Mic-Tsai/Power_Consumption_Current_Sense_System-V2/example/Python_Plot/ex1/ch1_iload-1111.png

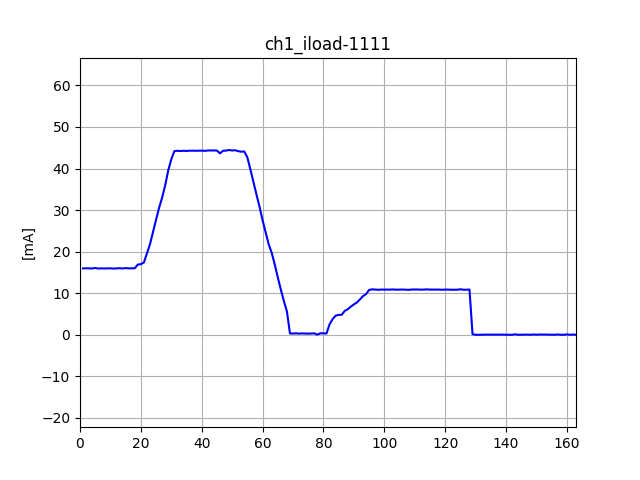
example/Python_Plot/ex1/ch1_iload-1111.png
