Mic-Tsai/Power_Consumption_Current_Sense_System-V2/res/ch1_iload.png

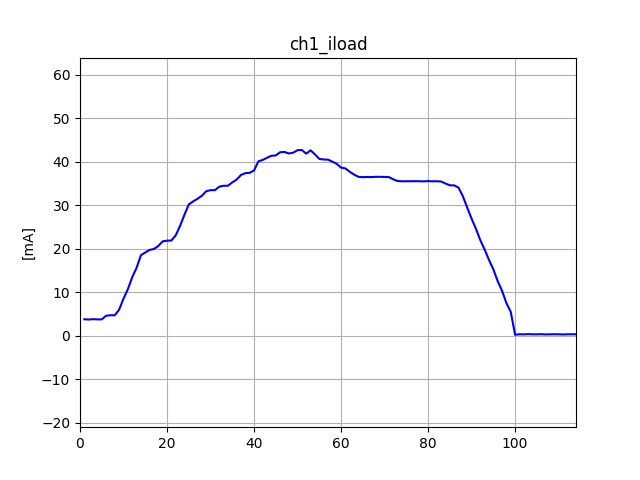
res/ch1_iload.png
